Pontifex42/Halloween-Coffin/Media/BottomView.jpg

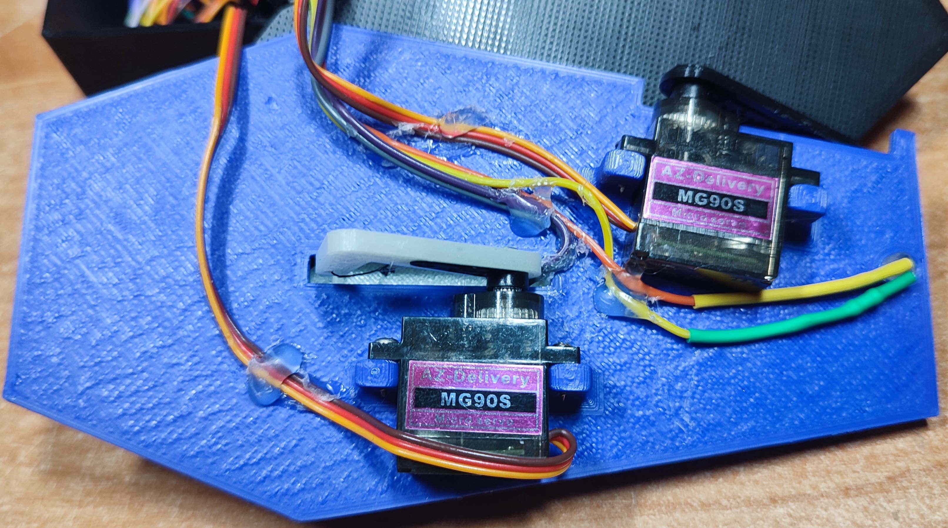
Media/BottomView.jpg
