Pontifex42/Halloween-Coffin/Media/CoverHinge.jpg

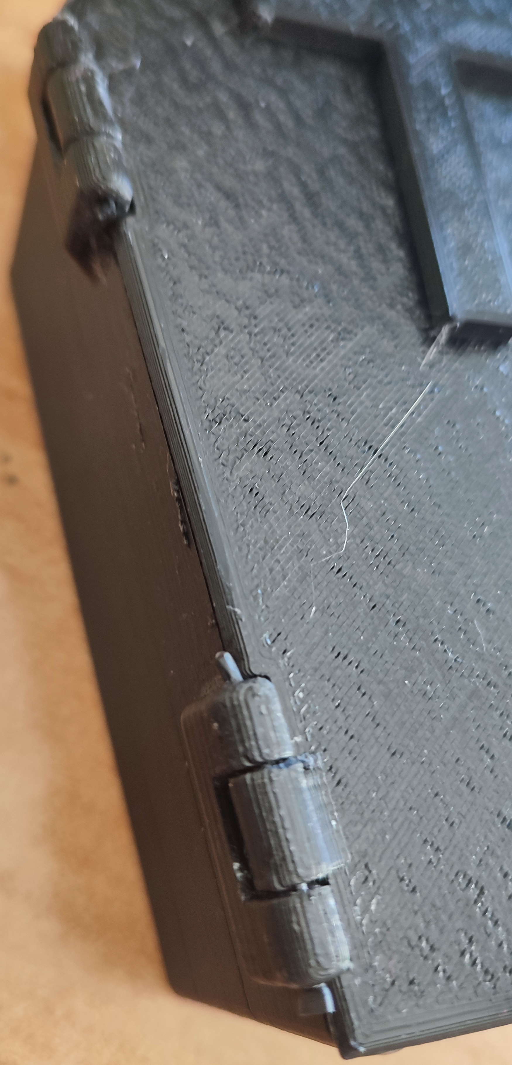
Media/CoverHinge.jpg
