Pontifex42/Halloween-Coffin/Media/InnerView2.jpg

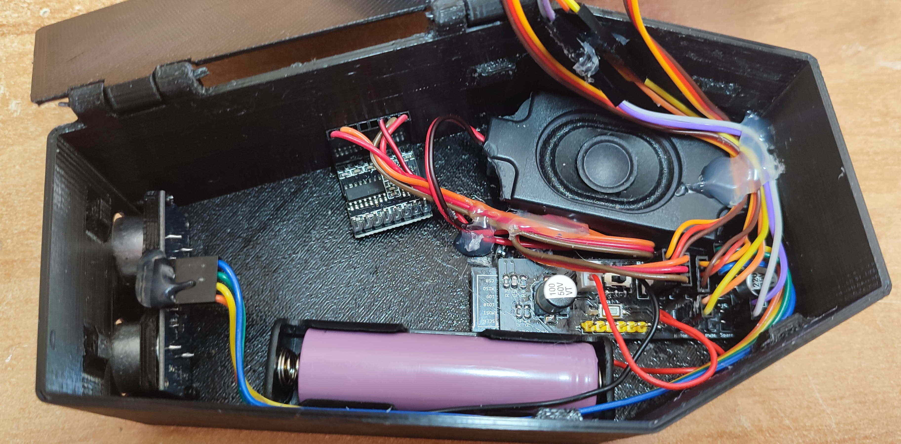
Media/InnerView2.jpg
