Pontifex42/Halloween-Coffin/Media/InnerView3.jpg

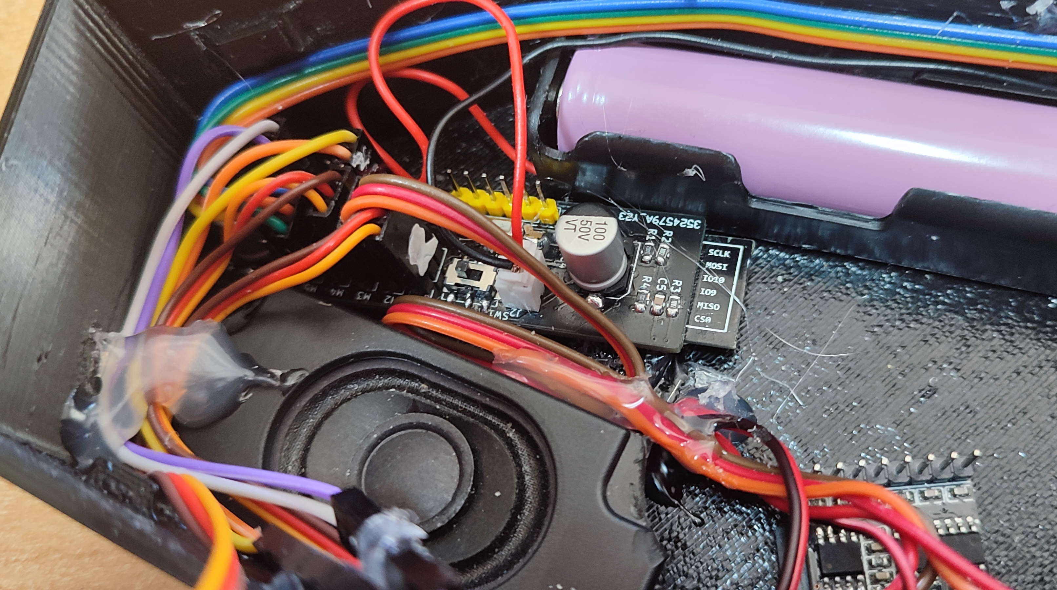
Media/InnerView3.jpg
