Pontifex42/Halloween-Coffin/Media/NightView.jpg

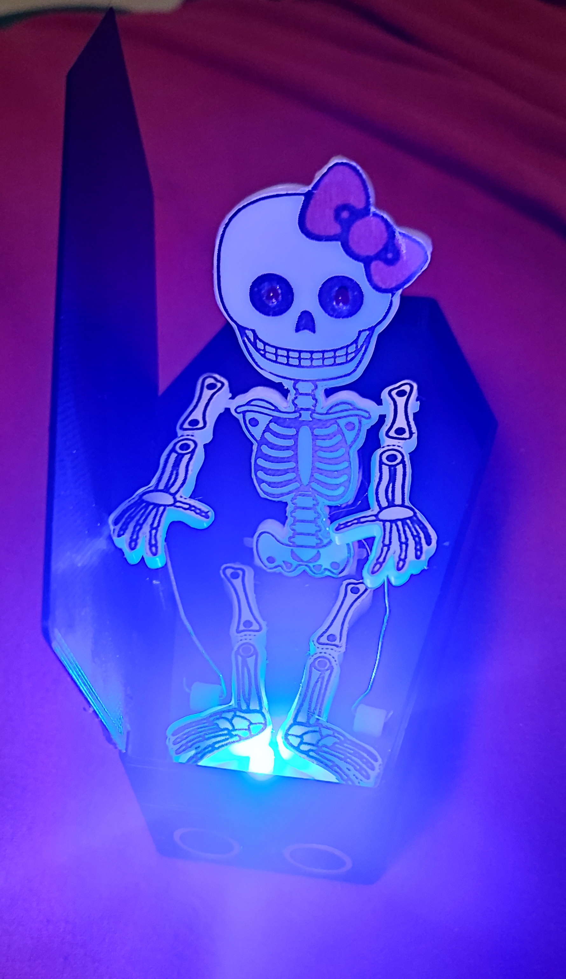
Media/NightView.jpg
