Pontifex42/Halloween-Coffin/Code/UniMini ESP8266/HalloweenCoffin/CoffinMP3Player.h

#pragma once

void SetupMP3Player();
void LoopMP3Player();

#define KNARREN 1
#define WANTYOUTODIE 2
#define TODESSCHREI 3
#define SCHREI 4
#define KNARREN2 5
#define BRUELL 6
#define BRUELL2 7
#define GESPENST 8
#define GLOCKENSCHLAG 9
#define GOTTISTTOT 10
#define INDERSTILLE 11
#define JESUSHIERISTNINA 12
#define KICHERN 13
#define KLEINERVAMPI 14
#define KRAEHE 15
#define MEINGERIPPE 16
#define TOTTUTNOT 17
#define UNDWIRBEISSEN 18
#define WOLF1 19
#define WOLF2 20
void CoffinPlayMP3(int no);
